Tuplanolla/hose-clamp/concave-clamp.png

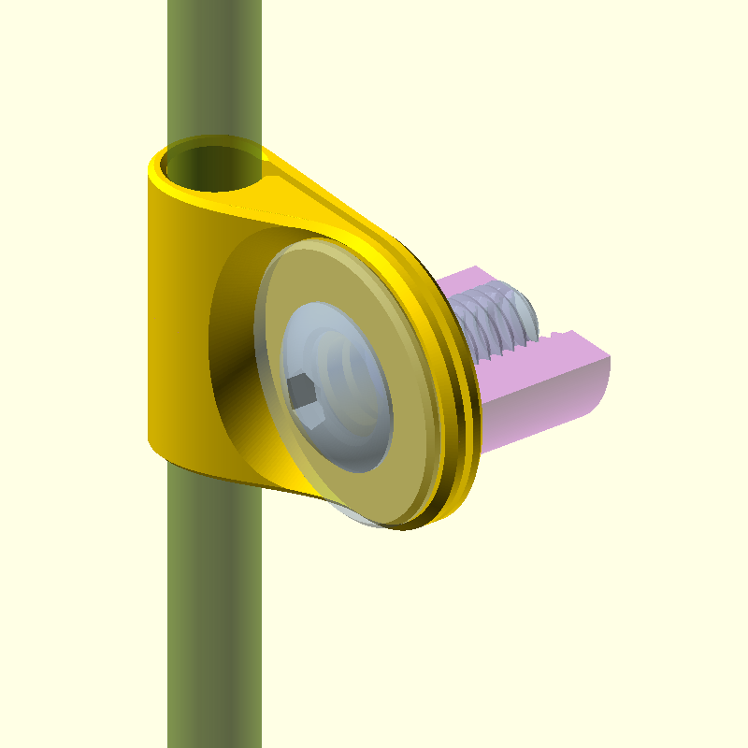
concave-clamp.png
