Tuplanolla/hose-clamp/long-clamp.png

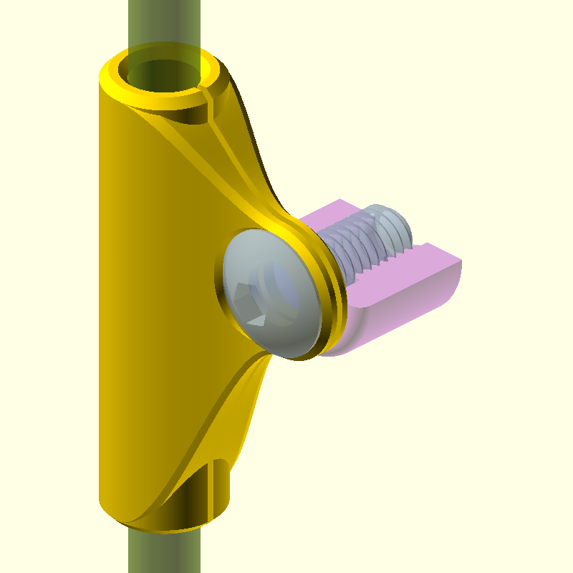
long-clamp.png
